reiser4/amc/eagle_file/egle_pdf/MODULO0.pdf

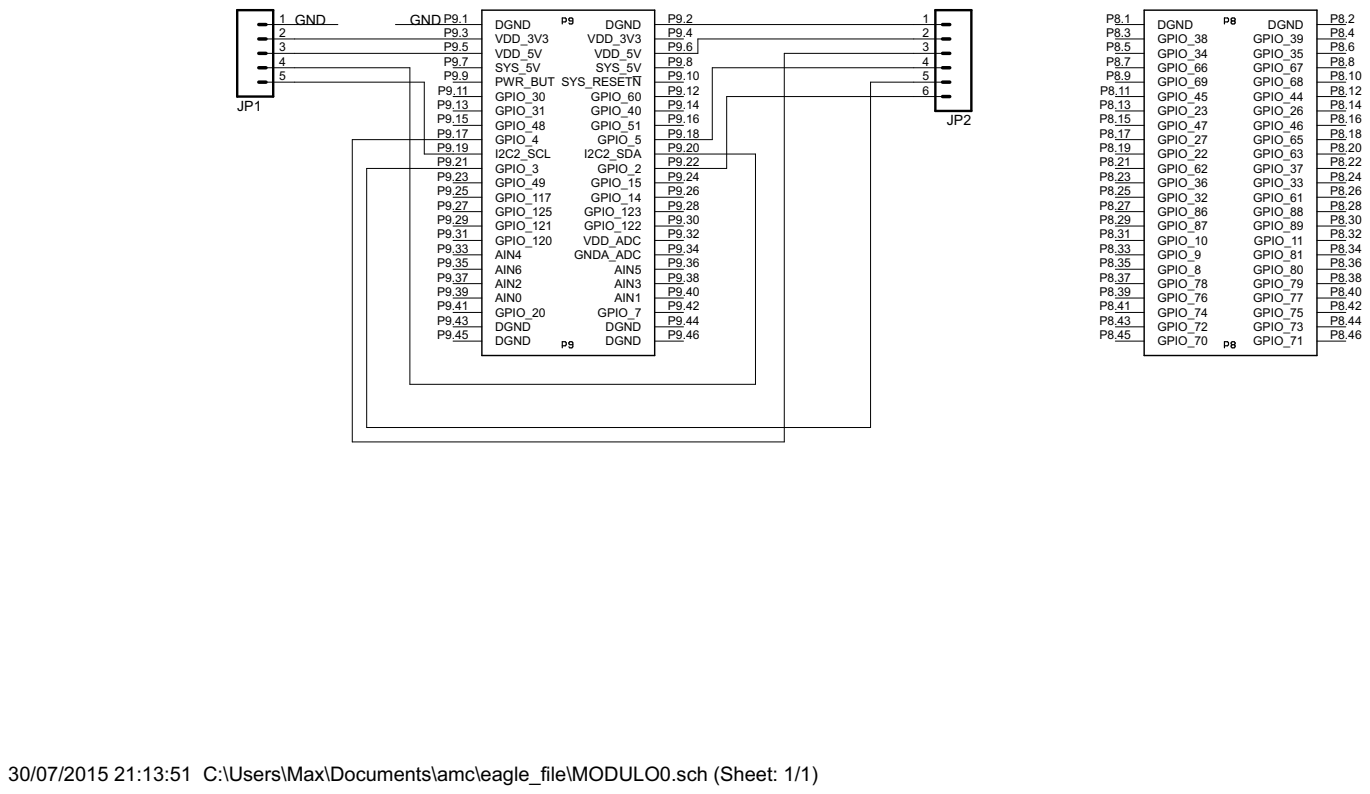
[picture p16: page 1]

30/07/2015 21:13:51 C:\Users\Max\Documents\amc\eagle_file\MODULO0.sch (Sheet: 1/1)
