reiser4/amc/eagle_file/egle_pdf/MODULO0_brd.pdf

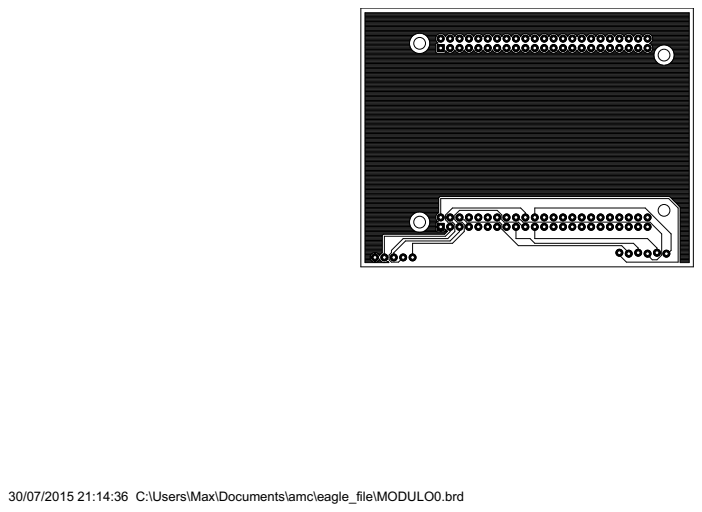
[picture p17: page 1]

30/07/2015 21:14:36 C:\Users\Max\Documents\amc\eagle_file\MODULO0.brd
