reiser4/amc/eagle_file/egle_pdf/MODULO1.pdf

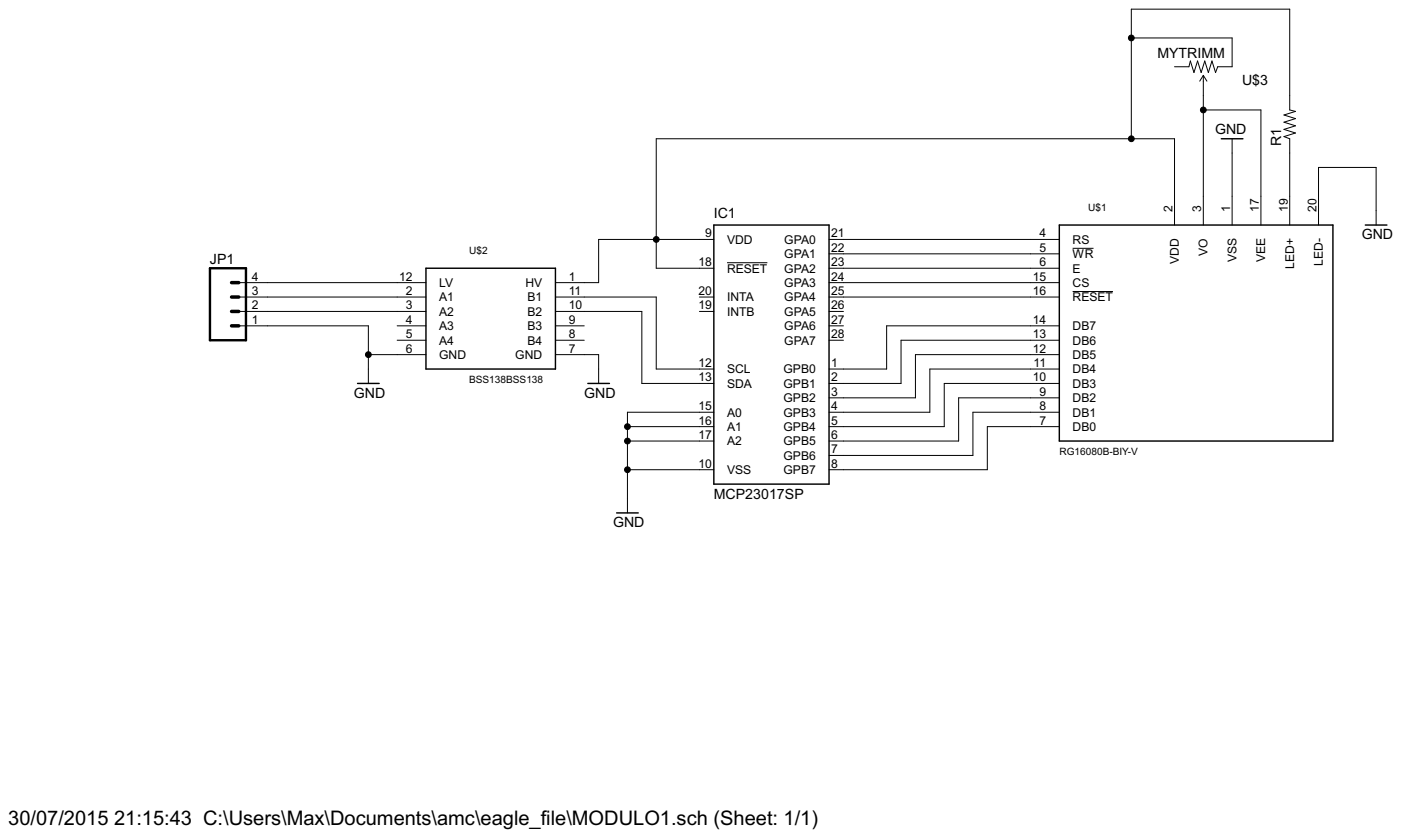
[picture p18: page 1]

30/07/2015 21:15:43 C:\Users\Max\Documents\amc\eagle_file\MODULO1.sch (Sheet: 1/1)
