reiser4/amc/eagle_file/egle_pdf/MODULO2_def.pdf

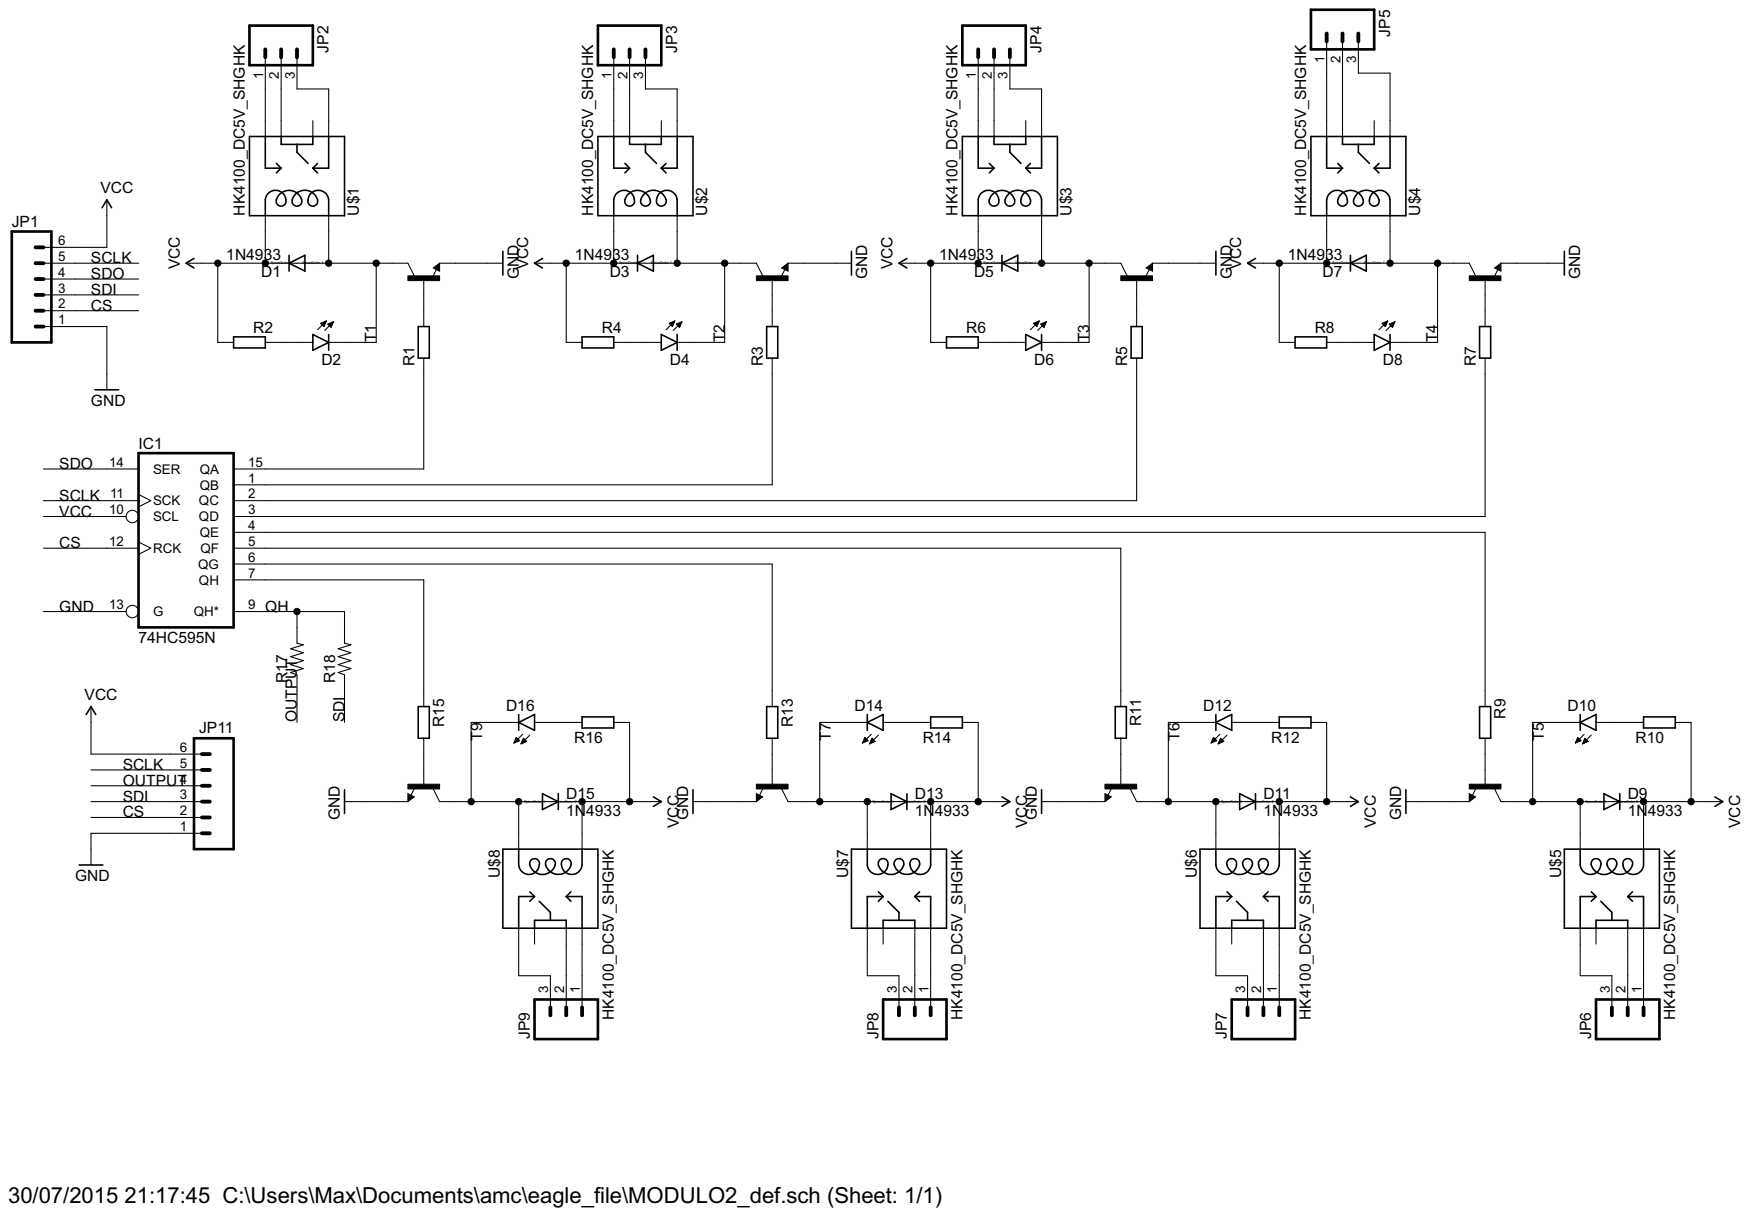
[picture p19: page 1]

30/07/2015 21:17:45 C:\Users\Max\Documents\amc\eagle_file\MODULO2_def.sch (Sheet: 1/1)
