reiser4/amc/ioloop/bcdin.py

### BCD IN
# funzionamento: questo modulo legge lo stato dei piedini e fornisce la lettura della banda selezionata



class BcdIn:

	def __init__(self, pinA, pinB, pinC, pinD):
		self.pinA = pinA
		self.pinB = pinB
		self.pinC = pinC
		self.pinD = pinD


	def readBand():
		print "Non implementato"
